tobsec/eidothea/etb-9201.kicad_sch

## KiCad design etb-9201.kicad_sch (2023-04-28)

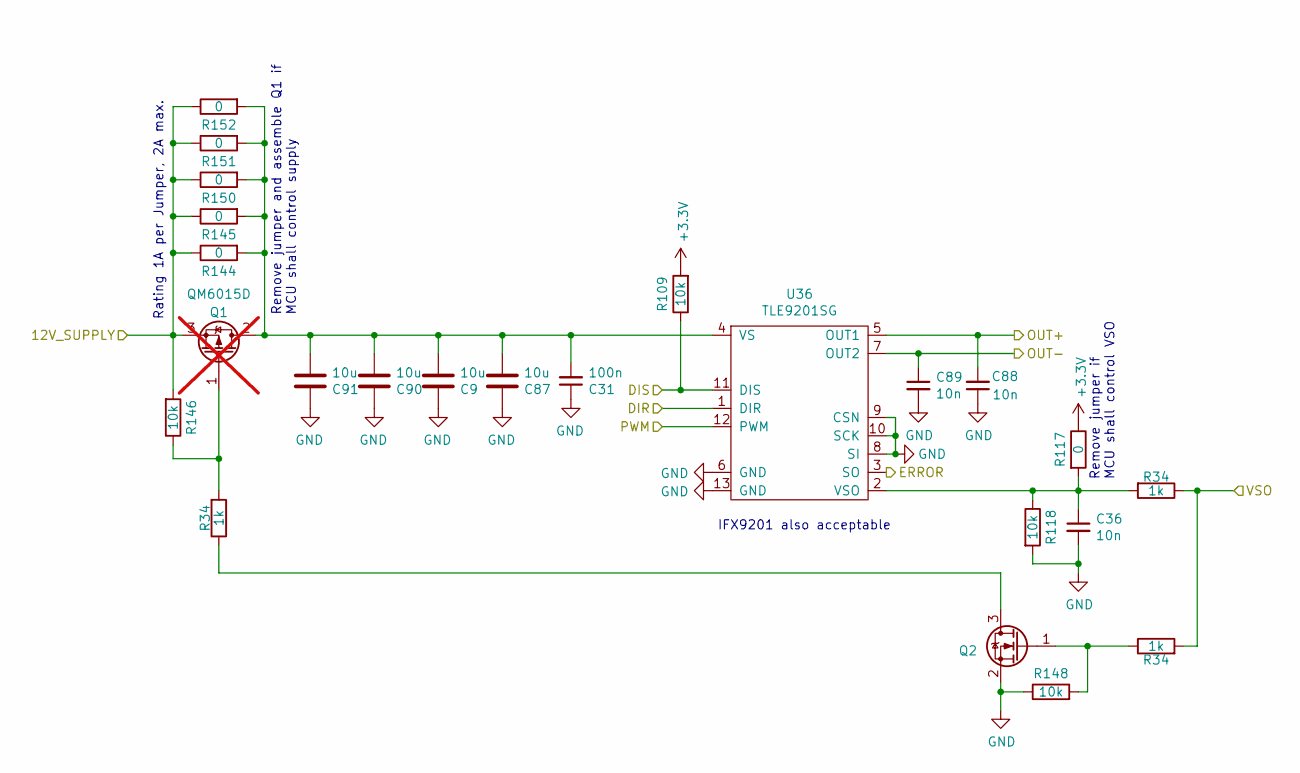
[picture p22: schematic etb-9201.kicad_sch]

Parts:
C9, C87, C90, C91: 10u; C_1206_3216Metric; LCSC C13585
C31: 100n; C_0603_1608Metric; LCSC C14663
C36, C88, C89: 10n; C_0603_1608Metric; LCSC C57112
Q1: QM6015D; TO-252-2; not fitted
Q2: 2N7002; SOT-23; LCSC C8545
R34: 1k; R_0402_1005Metric; LCSC C11702
R109, R118, R146, R148: 10k; R_0402_1005Metric; LCSC C25744
R117, R144, R145, R150, R151, R152: 0; R_0402_1005Metric; LCSC C17168
U36: TLE9201SG; Infineon_PG-DSO-12-9_ThermalVias; LCSC C112633

Connections:
12V_SUPPLY: Q1.3 (S), R144.1, R145.1, R146.2, R150.1, R151.1, R152.1
+3.3V: R109.2, R117.1
DIR: U36.1 (DIR)
DIS: R109.1, U36.11 (DIS)
ERROR: U36.3 (SO)
GND: C9.1, C31.1, C36.2, C87.1, C88.1, C89.2, C90.1, C91.1, Q2.2 (S), R118.2, R148.1, U36.6 (GND), U36.8 (SI), U36.9 (CSN), U36.10 (SCK), U36.13 (GND)
unnamed: C9.2, C31.2, C87.2, C90.2, C91.2, Q1.2 (D), R144.2, R145.2, R150.2, R151.2, R152.2, U36.4 (VS)
unnamed: C36.1, R34.2, R117.2, R118.1, U36.2 (VSO)
unnamed: Q1.1 (G), R34.2, R146.1
unnamed: Q2.1 (G), R34.1, R148.2
unnamed: Q2.3 (D), R34.1
OUT+: C88.2, U36.5 (OUT1)
OUT-: C89.1, U36.7 (OUT2)
PWM: U36.12 (PWM)
VSO: R34.1, R34.2

Notes on the sheet:
Remove jumper and assemble Q1 if MCU shall control supply
IFX9201 also acceptable
Rating 1A per Jumper, 2A max.
Remove jumper if MCU shall control VSO
