tobsec/eidothea/etbsupervisor.kicad_sch

## KiCad design etbsupervisor.kicad_sch (2023-04-28)

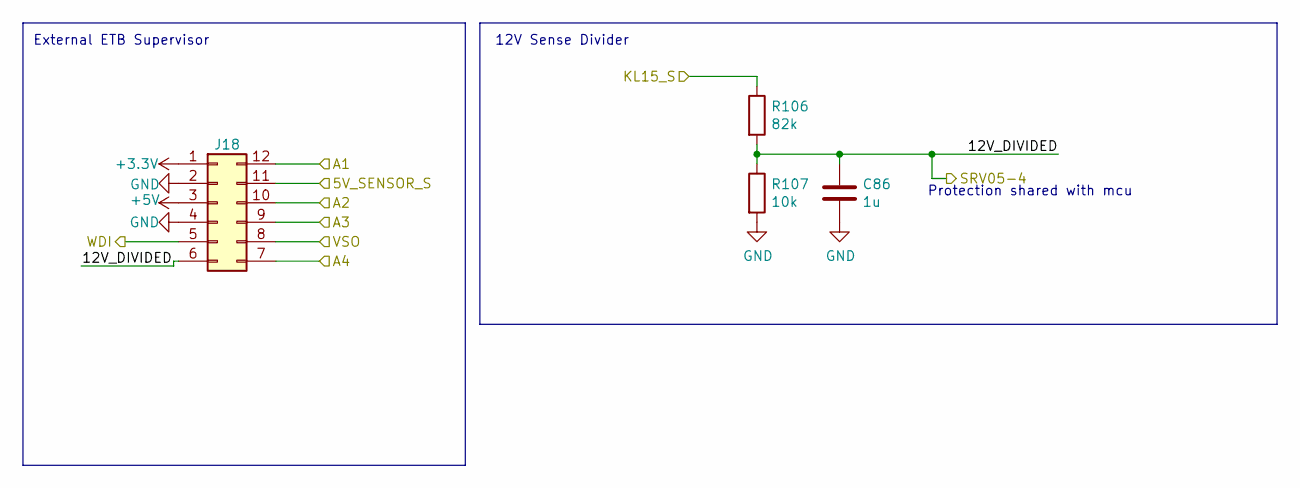
[picture p23: schematic etbsupervisor.kicad_sch]

Parts:
C86: 1u; C_0603_1608Metric; LCSC C15849
J18: Conn_02x04_Counter_Clockwise; PinHeader_2x06_P2.54mm_Vertical
R106: 82k; R_0603_1608Metric; LCSC C23254
R107: 10k; R_0402_1005Metric; LCSC C25744

Connections:
5V_SENSOR_S: J18.11
12V_DIVIDED: C86.1, J18.6, R106.2, R107.1
+3.3V: J18.1
+5V: J18.3
A1: J18.12
A2: J18.10
A3: J18.9
A4: J18.7
GND: C86.2, J18.2, J18.4, R107.2
KL15_S: R106.1
VSO: J18.8
WDI: J18.5

Notes on the sheet:
Protection shared with mcu
External ETB Supervisor
12V Sense Divider
