tobsec/eidothea/ign4.kicad_sch

## KiCad design ign4.kicad_sch (2023-04-26)

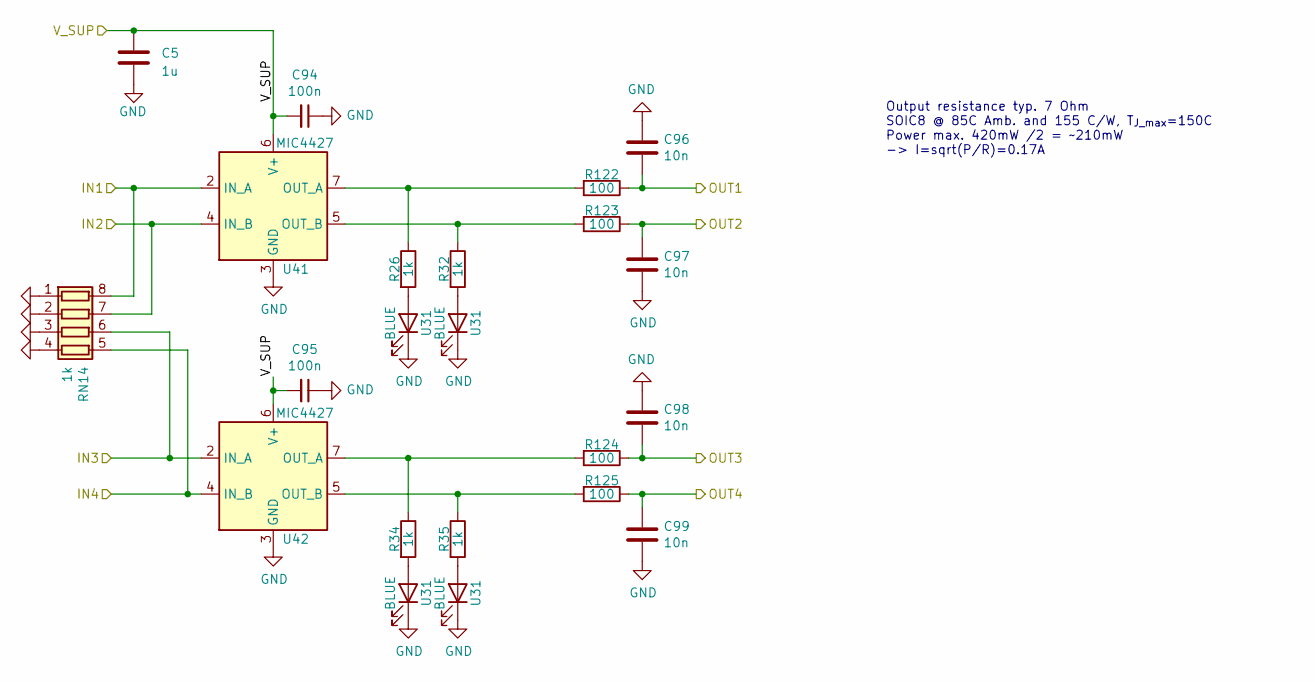
[picture p24: schematic ign4.kicad_sch]

Parts:
C5: 1u; C_0603_1608Metric; LCSC C15849
C94, C95: 100n; C_0603_1608Metric; LCSC C14663
C96, C97, C98, C99: 10n; C_0603_1608Metric; LCSC C57112
R26, R32, R34, R35: 1k; R_0402_1005Metric; LCSC C11702
R122, R123, R124, R125: 100; R_2512_6332Metric; LCSC C2907569
RN14: 1k; R_Array_Convex_4x0603; LCSC C20197
U31: BLUE; LED_0603_1608Metric; LCSC C72041
U41, U42: MIC4427; SOIC-8_3.9x4.9mm_P1.27mm; LCSC C20551

Connections:
GND: C5.1, C94.1, C95.1, C96.2, C97.2, C98.2, C99.2, RN14.1 (R1.1), RN14.2 (R2.1), RN14.3 (R3.1), RN14.4 (R4.1), U31.1 (K), U41.3 (GND), U42.3 (GND)
IN1: RN14.8 (R1.2), U41.2 (IN_A)
IN2: RN14.7 (R2.2), U41.4 (IN_B)
IN3: RN14.6 (R3.2), U42.2 (IN_A)
IN4: RN14.5 (R4.2), U42.4 (IN_B)
unnamed: R26.2, U31.2 (A)
unnamed: R32.2, U31.2 (A)
unnamed: R34.2, U31.2 (A)
unnamed: R35.2, U31.2 (A)
unnamed: R26.1, R122.2, U41.7 (OUT_A)
unnamed: R32.1, R123.2, U41.5 (OUT_B)
unnamed: R34.1, R124.2, U42.7 (OUT_A)
unnamed: R35.1, R125.2, U42.5 (OUT_B)
OUT1: C96.1, R122.1
OUT2: C97.1, R123.1
OUT3: C98.1, R124.1
OUT4: C99.1, R125.1
V_SUP: C5.2, C94.2, C95.2, U41.6 (V+), U42.6 (V+)

Notes on the sheet:
Output resistance typ. 7 Ohm SOIC8 @ 85C Amb. and 155 C/W, T_{J_max}=150C Power max. 420mW /2 = ~210mW -> I=sqrt(P/R)=0.17A
