tobsec/eidothea/knock.kicad_sch

## KiCad design knock.kicad_sch (2023-04-28)

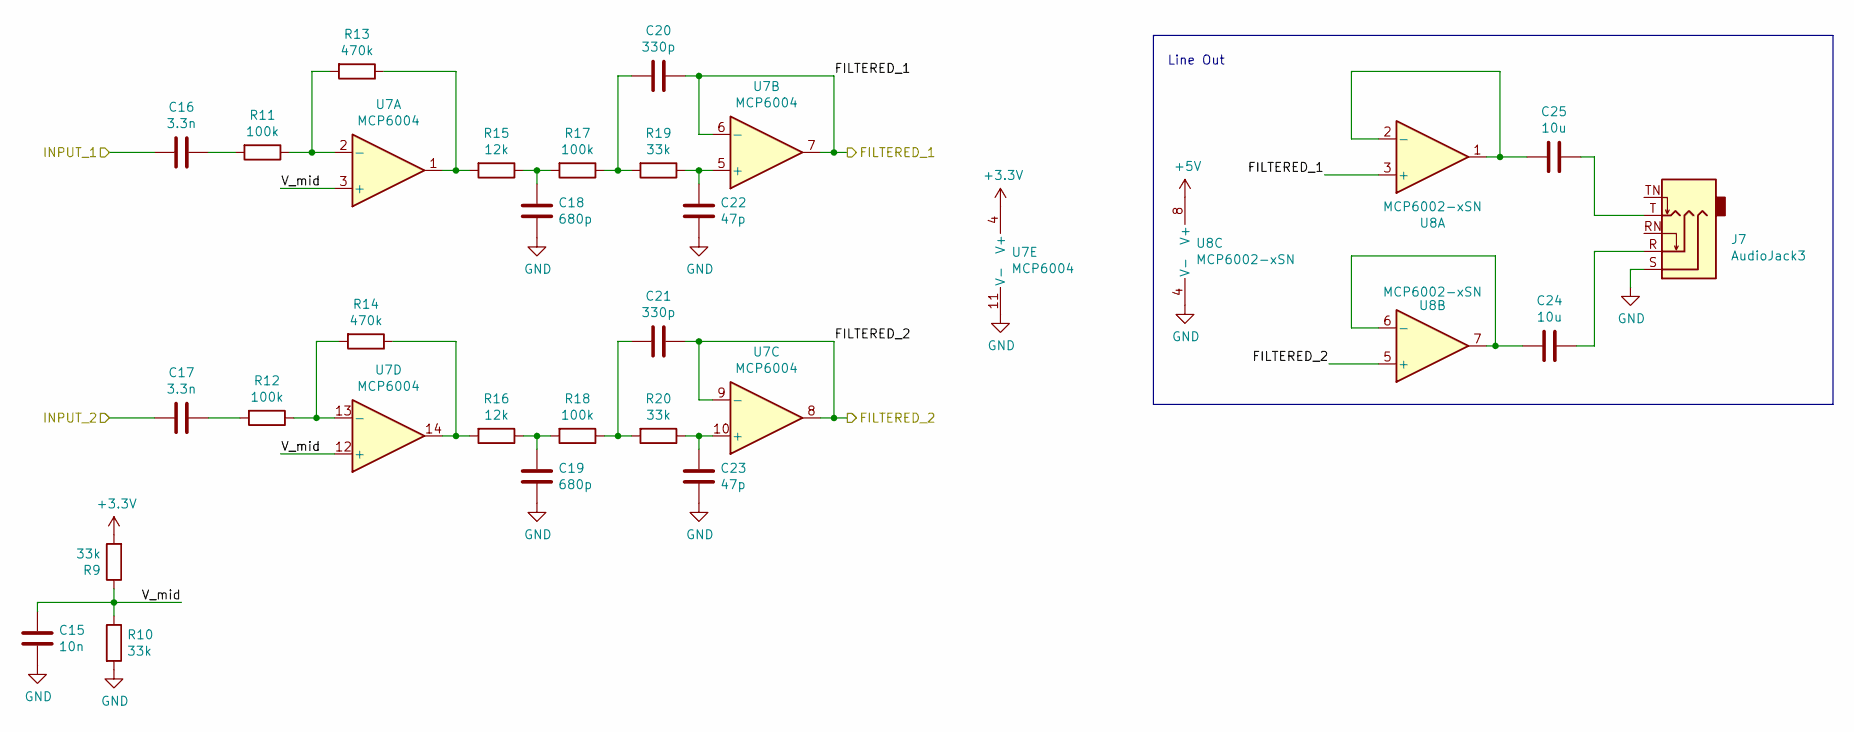
[picture p25: schematic knock.kicad_sch]

Parts:
C15: 10n; C_0603_1608Metric; LCSC C57112
C16, C17: 3.3n; C_0805_2012Metric; LCSC C107149
C18, C19: 680p; C_0603_1608Metric; LCSC C1630
C20, C21: 330p; C_0402_1005Metric; LCSC C13533
C22, C23: 47p; C_0402_1005Metric; LCSC C1567
C24, C25: 10u; C_1206_3216Metric; LCSC C13585
J7: AudioJack3; Jack_3.5mm_PJ-3250-5A; LCSC C165947
R9, R10, R19, R20: 33k; R_0402_1005Metric; LCSC C25779
R11, R12, R17, R18: 100k; R_0402_1005Metric; LCSC C25741
R13, R14: 470k; R_0402_1005Metric; LCSC C25790
R15, R16: 12k; R_0402_1005Metric; LCSC C25752
U7: MCP6004; TSSOP-14_4.4x5mm_P0.65mm; LCSC C50282
U8: MCP6002-xSN; SOIC-8_3.9x4.9mm_P1.27mm; LCSC C7377

Connections:
+3.3V: R9.2, U7.4 (V+)
+5V: U8.8 (V+)
FILTERED_1: C20.2, U7.6 (-), U7.7, U8.3 (+)
FILTERED_2: C21.2, U7.8, U7.9 (-), U8.5 (+)
GND: C15.1, C18.1, C19.1, C22.1, C23.1, J7.S, R10.2, U7.11 (V-), U8.4 (V-)
INPUT_1: C16.2
INPUT_2: C17.2
unnamed: C16.1, R11.2
unnamed: C17.1, R12.2
unnamed: C18.2, R15.1, R17.2
unnamed: C19.2, R16.1, R18.2
unnamed: C20.1, R17.1, R19.2
unnamed: C21.1, R18.1, R20.2
unnamed: C22.2, R19.1, U7.5 (+)
unnamed: C23.2, R20.1, U7.10 (+)
unnamed: C24.1, J7.R
unnamed: C24.2, U8.6 (-), U8.7
unnamed: C25.1, J7.T
unnamed: C25.2, U8.1, U8.2 (-)
unnamed: R11.1, R13.2, U7.2 (-)
unnamed: R12.1, R14.2, U7.13 (-)
unnamed: R13.1, R15.2, U7.1
unnamed: R14.1, R16.2, U7.14
V_mid: C15.2, R9.1, R10.1, U7.3 (+), U7.12 (+)

Notes on the sheet:
Line Out
