tobsec/eidothea/lowside_dual.kicad_sch

## KiCad design lowside_dual.kicad_sch (2023-04-28)

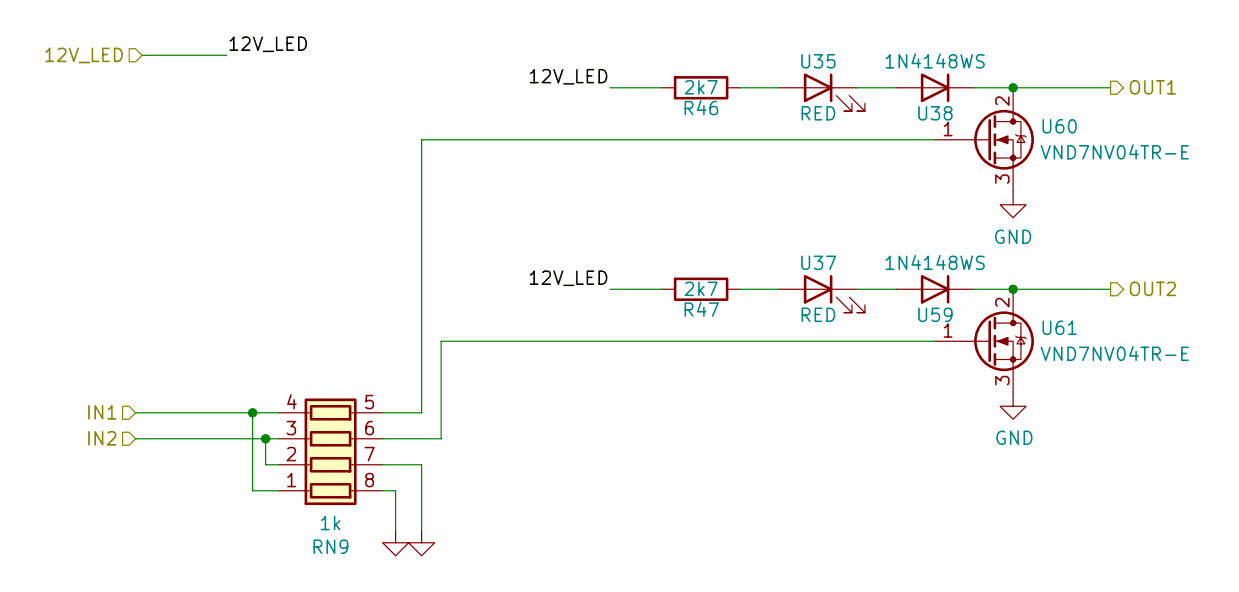
[picture p26: schematic lowside_dual.kicad_sch]

Parts:
R46, R47: 2k7; R_0402_1005Metric; LCSC C138017
RN9: 1k; R_Array_Convex_4x0603; LCSC C20197
U35, U37: RED; LED_0603_1608Metric; LCSC C2286
U38, U59: 1N4148WS; D_SOD-323; LCSC C2128
U60, U61: VND7NV04TR-E; TO-252-3_TabPin2; LCSC C262999

Connections:
12V_LED: R46.2, R47.2
GND: RN9.7 (R2.2), RN9.8 (R1.2), U60.3 (S), U61.3 (S)
IN1: RN9.1 (R1.1), RN9.4 (R4.1)
IN2: RN9.2 (R2.1), RN9.3 (R3.1)
unnamed: R46.1, U35.2 (A)
unnamed: R47.1, U37.2 (A)
unnamed: RN9.5 (R4.2), U60.1 (G)
unnamed: RN9.6 (R3.2), U61.1 (G)
unnamed: U35.1 (K), U38.2 (A)
unnamed: U37.1 (K), U59.2 (A)
OUT1: U38.1 (K), U60.2 (D)
OUT2: U59.1 (K), U61.2 (D)
