tobsec/eidothea/lowside_quad.kicad_sch

## KiCad design lowside_quad.kicad_sch (2023-04-28)

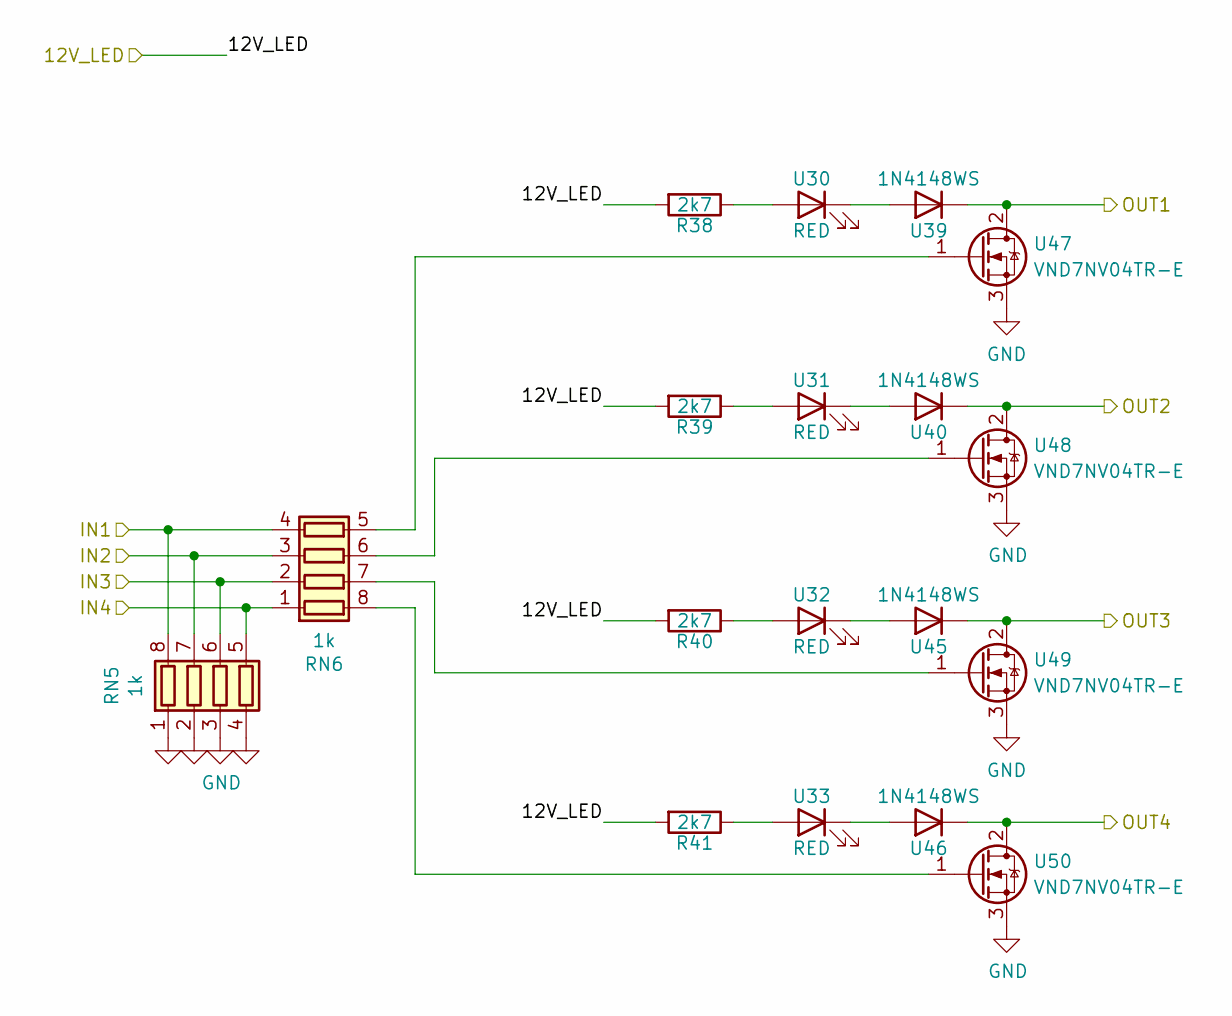
[picture p27: schematic lowside_quad.kicad_sch]

Parts:
R38, R39, R40, R41: 2k7; R_0402_1005Metric; LCSC C138017
RN5, RN6: 1k; R_Array_Convex_4x0603; LCSC C20197
U30, U31, U32, U33: RED; LED_0603_1608Metric; LCSC C2286
U39, U40, U45, U46: 1N4148WS; D_SOD-323; LCSC C2128
U47, U48, U49, U50: VND7NV04TR-E; TO-252-3_TabPin2; LCSC C262999

Connections:
12V_LED: R38.2, R39.2, R40.2, R41.2
GND: RN5.1 (R1.1), RN5.2 (R2.1), RN5.3 (R3.1), RN5.4 (R4.1), U47.3 (S), U48.3 (S), U49.3 (S), U50.3 (S)
IN1: RN5.8 (R1.2), RN6.4 (R4.1)
IN2: RN5.7 (R2.2), RN6.3 (R3.1)
IN3: RN5.6 (R3.2), RN6.2 (R2.1)
IN4: RN5.5 (R4.2), RN6.1 (R1.1)
unnamed: R38.1, U30.2 (A)
unnamed: R39.1, U31.2 (A)
unnamed: R40.1, U32.2 (A)
unnamed: R41.1, U33.2 (A)
unnamed: RN6.5 (R4.2), U47.1 (G)
unnamed: RN6.6 (R3.2), U48.1 (G)
unnamed: RN6.7 (R2.2), U49.1 (G)
unnamed: RN6.8 (R1.2), U50.1 (G)
unnamed: U30.1 (K), U39.2 (A)
unnamed: U31.1 (K), U40.2 (A)
unnamed: U32.1 (K), U45.2 (A)
unnamed: U33.1 (K), U46.2 (A)
OUT1: U39.1 (K), U47.2 (D)
OUT2: U40.1 (K), U48.2 (D)
OUT3: U45.1 (K), U49.2 (D)
OUT4: U46.1 (K), U50.2 (D)
