tobsec/eidothea/lowside_uln2003.kicad_sch

## KiCad design lowside_uln2003.kicad_sch (2023-04-26)

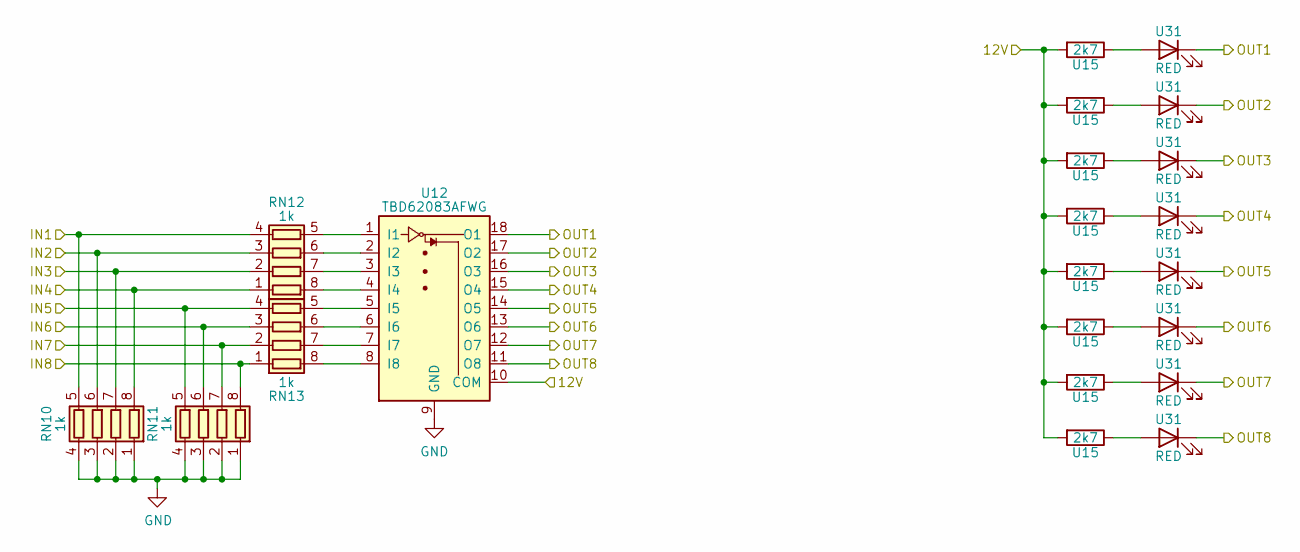
[picture p28: schematic lowside_uln2003.kicad_sch]

Parts:
RN10, RN11, RN12, RN13: 1k; R_Array_Convex_4x0603; LCSC C20197
U12: TBD62083AFWG; SOIC-18W_7.5x11.6mm_P1.27mm
U15: 2k7; R_0402_1005Metric; LCSC C138017
U31: RED; LED_0603_1608Metric; LCSC C2286

Connections:
12V: U12.10 (COM), U15.2
GND: RN10.1 (R1.1), RN10.2 (R2.1), RN10.3 (R3.1), RN10.4 (R4.1), RN11.1 (R1.1), RN11.2 (R2.1), RN11.3 (R3.1), RN11.4 (R4.1), U12.9 (GND)
IN1: RN10.5 (R4.2), RN12.4 (R4.1)
IN2: RN10.6 (R3.2), RN12.3 (R3.1)
IN3: RN10.7 (R2.2), RN12.2 (R2.1)
IN4: RN10.8 (R1.2), RN12.1 (R1.1)
IN5: RN11.5 (R4.2), RN13.4 (R4.1)
IN6: RN11.6 (R3.2), RN13.3 (R3.1)
IN7: RN11.7 (R2.2), RN13.2 (R2.1)
IN8: RN11.8 (R1.2), RN13.1 (R1.1)
unnamed: RN12.5 (R4.2), U12.1 (I1)
unnamed: RN12.6 (R3.2), U12.2 (I2)
unnamed: RN12.7 (R2.2), U12.3 (I3)
unnamed: RN12.8 (R1.2), U12.4 (I4)
unnamed: RN13.5 (R4.2), U12.5 (I5)
unnamed: RN13.6 (R3.2), U12.6 (I6)
unnamed: RN13.7 (R2.2), U12.7 (I7)
unnamed: RN13.8 (R1.2), U12.8 (I8)
unnamed: U15.1, U31.2 (A)
OUT1: U12.18 (O1), U31.1 (K)
OUT2: U12.17 (O2), U31.1 (K)
OUT3: U12.16 (O3), U31.1 (K)
OUT4: U12.15 (O4), U31.1 (K)
OUT5: U12.14 (O5), U31.1 (K)
OUT6: U12.13 (O6), U31.1 (K)
OUT7: U12.12 (O7), U31.1 (K)
OUT8: U12.11 (O8), U31.1 (K)
