tobsec/eidothea/mcu.kicad_sch

## KiCad design mcu.kicad_sch (2023-04-28)

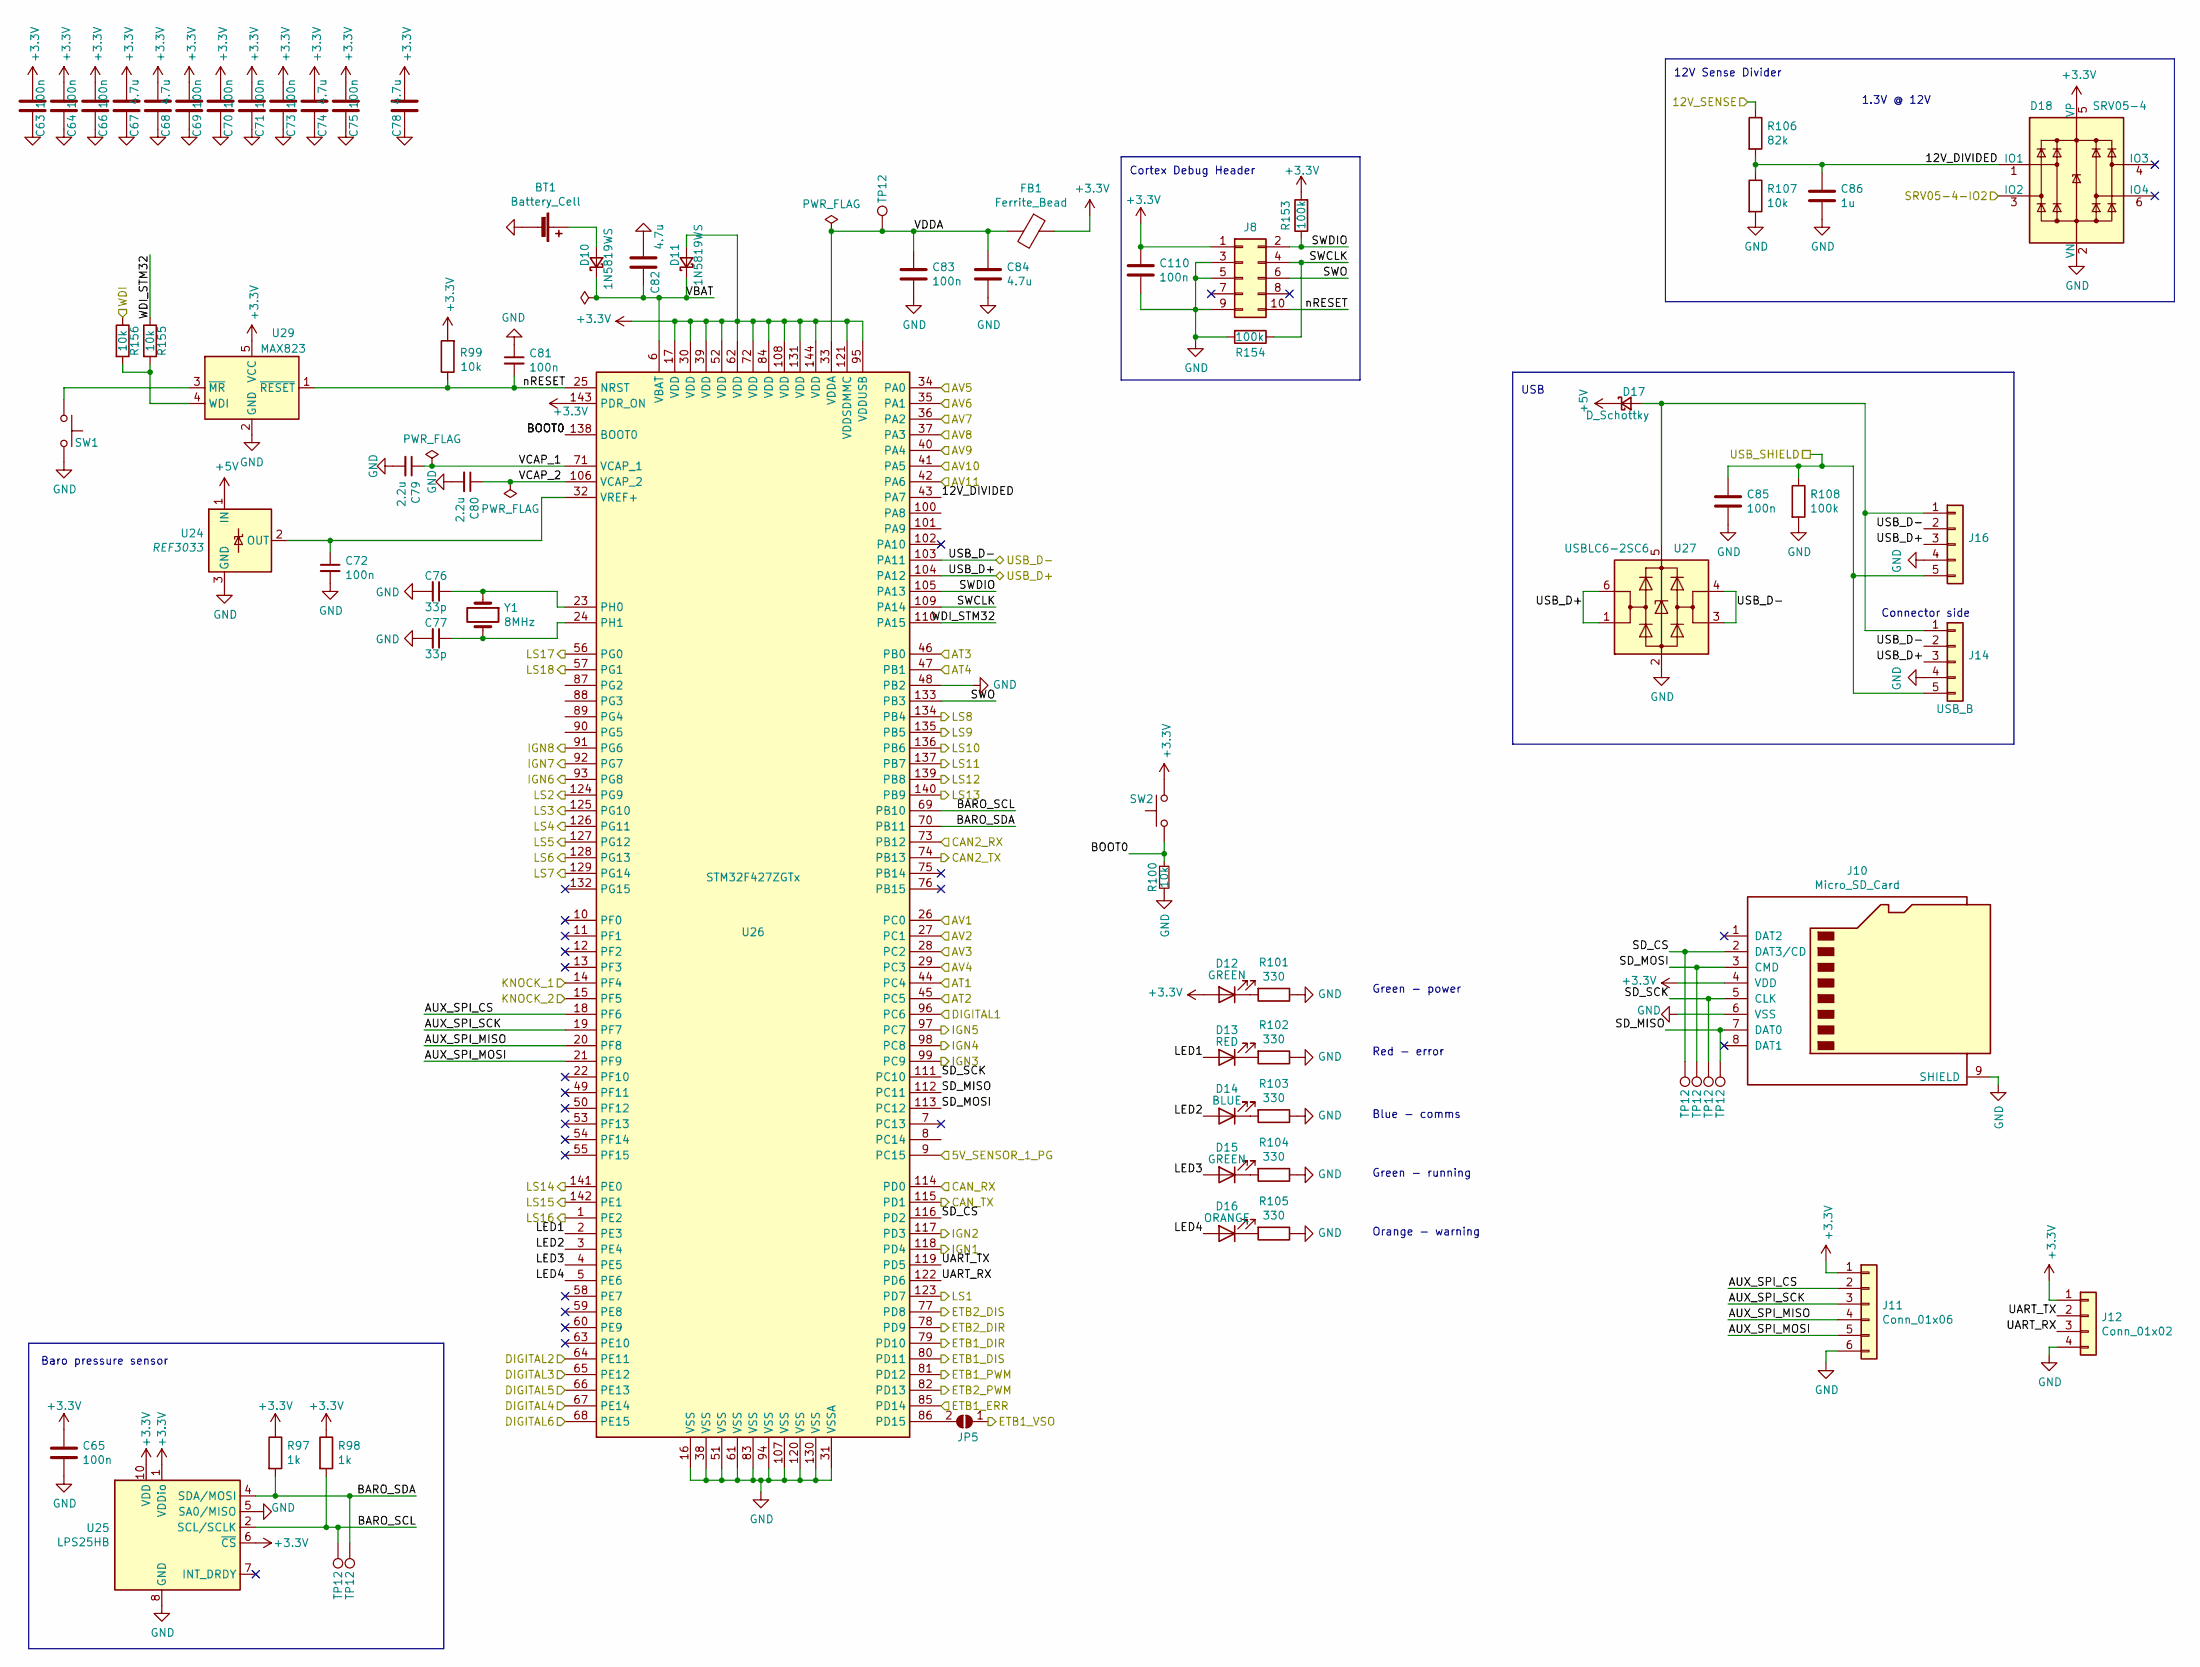
[picture p29: schematic mcu.kicad_sch]

Parts:
BT1: Battery_Cell; BatteryHolder_Keystone_1060_1x2032; LCSC C70377
C63, C64, C65, C66, C69, C70, C71, C72, C73, C75, C81, C83, C85, C110: 100n; C_0603_1608Metric; LCSC C14663
C67, C68, C74, C78, C82, C84: 4.7u; C_0603_1608Metric; LCSC C19666
C76, C77: 33p; C_0402_1005Metric; LCSC C1562
C79, C80: 2.2u; C_0603_1608Metric; LCSC C23630
C86: 1u; C_0603_1608Metric; LCSC C15849
D10, D11: 1N5819WS; D_SOD-323; LCSC C191023
D12, D15: GREEN; LED_0603_1608Metric; LCSC C72043
D13: RED; LED_0603_1608Metric; LCSC C2286
D14: BLUE; LED_0603_1608Metric; LCSC C72041
D16: ORANGE; LED_0603_1608Metric; LCSC C72038
D17: D_Schottky; D_SMA; LCSC C14996
D18: SRV05-4; SOT-23-6; LCSC C85364
FB1: Ferrite_Bead; L_0805_2012Metric; LCSC C1015
J8: Conn_02x05_Odd_Even; PinHeader_2x05_P2.54mm_Vertical; LCSC N/A
J10: Micro_SD_Card; microSD_HC_Wuerth_693072010801; LCSC C164170
J11: Conn_01x06; PinHeader_1x06_P2.54mm_Vertical; LCSC N/A
J12: Conn_01x02; PinHeader_1x04_P2.54mm_Vertical; LCSC N/A
J14: USB_B; USB_B_921-111A1010Y10200_Vertical; LCSC C26234
J16: PinHeader_1x05_P2.54mm_Vertical; JLCPosOffset -1.27,-2.1
JP5: Jumper_2_Bridged; SolderJumper-2_P1.3mm_Open_RoundedPad1.0x1.5mm
R97, R98: 1k; R_0402_1005Metric; LCSC C11702
R99, R100, R107, R155, R156: 10k; R_0402_1005Metric; LCSC C25744
R101, R102, R103, R104, R105: 330; R_0402_1005Metric; LCSC C25104
R106: 82k; R_0603_1608Metric; LCSC C23254
R108, R153, R154: 100k; R_0402_1005Metric; LCSC C25741
SW1, SW2: SW_Push; SW_SPST_EVQQ2; LCSC C318884
TP12: TestPoint; TestPoint_Pad_D1.0mm
U24: REF3033; SOT-23; LCSC C36658
U25: LPS25HB; ST_HLGA-10_2.5x2.5mm_P0.6mm_LayoutBorder3x2y; LCSC C94049
U26: STM32F427ZGTx; LQFP-144_20x20mm_P0.5mm; LCSC C117816
U27: USBLC6-2SC6; SOT-23-6; LCSC C7519
U29: MAX823; SOT-23-5; LCSC C239902
Y1: 8MHz; Crystal_SMD_5032-2Pin_5.0x3.2mm; LCSC C115962

Connections:
5V_SENSOR_1_PG: U26.9 (PC15)
12V_DIVIDED: C86.1, D18.1 (IO1), R106.2, R107.1, U26.43 (PA7)
12V_SENSE: R106.1
+3.3V: C63.2, C64.2, C65.1, C66.2, C67.2, C68.2, C69.2, C70.2, C71.2, C73.2, C74.2, C75.2, C78.2, C110.1, D11.2 (A), D12.2 (A), D18.5 (VP), FB1.1, J8.1, J10.4 (VDD), J11.1, J12.1, R97.1, R98.1, R99.2, R153.2, SW2.2, U25.1 (VDDio), U25.6 (~CS), U25.10 (VDD), U26.17 (VDD), U26.30 (VDD), U26.39 (VDD), U26.52 (VDD), U26.62 (VDD), U26.72 (VDD), U26.84 (VDD), U26.95 (VDDUSB), U26.108 (VDD), U26.121 (VDDSDMMC), U26.131 (VDD), U26.143 (PDR_ON), U26.144 (VDD), U29.5 (VCC)
+5V: D17.1 (K), U24.1 (IN)
AT1: U26.44 (PC4)
AT2: U26.45 (PC5)
AT3: U26.46 (PB0)
AT4: U26.47 (PB1)
AUX_SPI_CS: J11.2, U26.18 (PF6)
AUX_SPI_MISO: J11.4, U26.20 (PF8)
AUX_SPI_MOSI: J11.5, U26.21 (PF9)
AUX_SPI_SCK: J11.3, U26.19 (PF7)
AV1: U26.26 (PC0)
AV2: U26.27 (PC1)
AV3: U26.28 (PC2)
AV4: U26.29 (PC3)
AV5: U26.34 (PA0)
AV6: U26.35 (PA1)
AV7: U26.36 (PA2)
AV8: U26.37 (PA3)
AV9: U26.40 (PA4)
AV10: U26.41 (PA5)
AV11: U26.42 (PA6)
BARO_SCL: R98.2, TP12.1, U25.2 (SCL/SCLK), U26.69 (PB10)
BARO_SDA: R97.2, TP12.1, U25.4 (SDA/MOSI), U26.70 (PB11)
BOOT0: R100.1, SW2.1, U26.138 (BOOT0)
CAN2_RX: U26.73 (PB12)
CAN2_TX: U26.74 (PB13)
CAN_RX: U26.114 (PD0)
CAN_TX: U26.115 (PD1)
DIGITAL1: U26.96 (PC6)
DIGITAL2: U26.64 (PE11)
DIGITAL3: U26.65 (PE12)
DIGITAL4: U26.67 (PE14)
DIGITAL5: U26.66 (PE13)
DIGITAL6: U26.68 (PE15)
ETB1_DIR: U26.79 (PD10)
ETB1_DIS: U26.80 (PD11)
ETB1_ERR: U26.85 (PD14)
ETB1_PWM: U26.81 (PD12)
ETB1_VSO: JP5.1 (A)
ETB2_DIR: U26.78 (PD9)
ETB2_DIS: U26.77 (PD8)
ETB2_PWM: U26.82 (PD13)
GND: BT1.2 (-), C63.1, C64.1, C65.2, C66.1, C67.1, C68.1, C69.1, C70.1, C71.1, C72.2, C73.1, C74.1, C75.1, C76.2, C77.2, C78.1, C79.2, C80.2, C81.1, C82.2, C83.2, C84.2, C85.2, C86.2, C110.2, D18.2 (VN), J8.3, J8.5, J8.9, J10.6 (VSS), J10.9 (SHIELD), J11.6, J12.4, J14.4, J16.4, R100.2, R101.1, R102.1, R103.1, R104.1, R105.1, R107.2, R108.2, R154.2, SW1.2, U24.3 (GND), U25.3 (GND), U25.5 (SA0/MISO), U25.8 (GND), U25.9 (GND), U26.16 (VSS), U26.31 (VSSA), U26.38 (VSS), U26.48 (PB2), U26.51 (VSS), U26.61 (VSS), U26.83 (VSS), U26.94 (VSS), U26.107 (VSS), U26.120 (VSS), U26.130 (VSS), U27.2 (GND), U29.2 (GND)
IGN1: U26.118 (PD4)
IGN2: U26.117 (PD3)
IGN3: U26.99 (PC9)
IGN4: U26.98 (PC8)
IGN5: U26.97 (PC7)
IGN6: U26.93 (PG8)
IGN7: U26.92 (PG7)
IGN8: U26.91 (PG6)
KNOCK_1: U26.14 (PF4)
KNOCK_2: U26.15 (PF5)
LED1: D13.2 (A), U26.2 (PE3)
LED2: D14.2 (A), U26.3 (PE4)
LED3: D15.2 (A), U26.4 (PE5)
LED4: D16.2 (A), U26.5 (PE6)
LS1: U26.123 (PD7)
LS2: U26.124 (PG9)
LS3: U26.125 (PG10)
LS4: U26.126 (PG11)
LS5: U26.127 (PG12)
LS6: U26.128 (PG13)
LS7: U26.129 (PG14)
LS8: U26.134 (PB4)
LS9: U26.135 (PB5)
LS10: U26.136 (PB6)
LS11: U26.137 (PB7)
LS12: U26.139 (PB8)
LS13: U26.140 (PB9)
LS14: U26.141 (PE0)
LS15: U26.142 (PE1)
LS16: U26.1 (PE2)
LS17: U26.56 (PG0)
LS18: U26.57 (PG1)
unnamed: BT1.1 (+), D10.2 (A)
unnamed: C72.1, U24.2 (OUT), U26.32 (VREF+)
unnamed: C76.1, U26.23 (PH0), Y1.1
unnamed: C77.1, U26.24 (PH1), Y1.2
unnamed: D12.1 (K), R101.2
unnamed: D13.1 (K), R102.2
unnamed: D14.1 (K), R103.2
unnamed: D15.1 (K), R104.2
unnamed: D16.1 (K), R105.2
unnamed: D17.2 (A), J14.1, J16.1, U27.5 (VBUS)
unnamed: JP5.2 (B), U26.86 (PD15)
unnamed: R155.2, R156.2, U29.4 (WDI)
unnamed: SW1.1, U29.3 (~MR)
SD_CS: J10.2 (DAT3/CD), TP12.1, U26.116 (PD2)
SD_MISO: J10.7 (DAT0), TP12.1, U26.112 (PC11)
SD_MOSI: J10.3 (CMD), TP12.1, U26.113 (PC12)
SD_SCK: J10.5 (CLK), TP12.1, U26.111 (PC10)
SRV05-4-IO2: D18.3 (IO2)
SWCLK: J8.4, R154.1, U26.109 (PA14)
SWDIO: J8.2, R153.1, U26.105 (PA13)
SWO: J8.6, U26.133 (PB3)
UART_RX: J12.3, U26.122 (PD6)
UART_TX: J12.2, U26.119 (PD5)
USB_D+: J14.3, J16.3, U26.104 (PA12), U27.1 (I/O1), U27.6 (I/O1)
USB_D-: J14.2, J16.2, U26.103 (PA11), U27.3 (I/O2), U27.4 (I/O2)
USB_SHIELD: C85.1, J14.5, J16.5, R108.1
VBAT: C82.1, D10.1 (K), D11.1 (K), U26.6 (VBAT)
VCAP_1: C79.1, U26.71 (VCAP_1)
VCAP_2: C80.1, U26.106 (VCAP_2)
VDDA: C83.1, C84.1, FB1.2, TP12.1, U26.33 (VDDA)
WDI: R156.1
WDI_STM32: R155.1, U26.110 (PA15)
nRESET: C81.2, J8.10, R99.1, U26.25 (NRST), U29.1 (~RESET)

Notes on the sheet:
Orange - warning
Connector side
USB
1.3V @ 12V
Cortex Debug Header
Baro pressure sensor
Blue - comms
Green - power
12V Sense Divider
Red - error
Green - running
