tobsec/eidothea/proteus.kicad_sch

## KiCad design proteus.kicad_sch (2023-04-28)

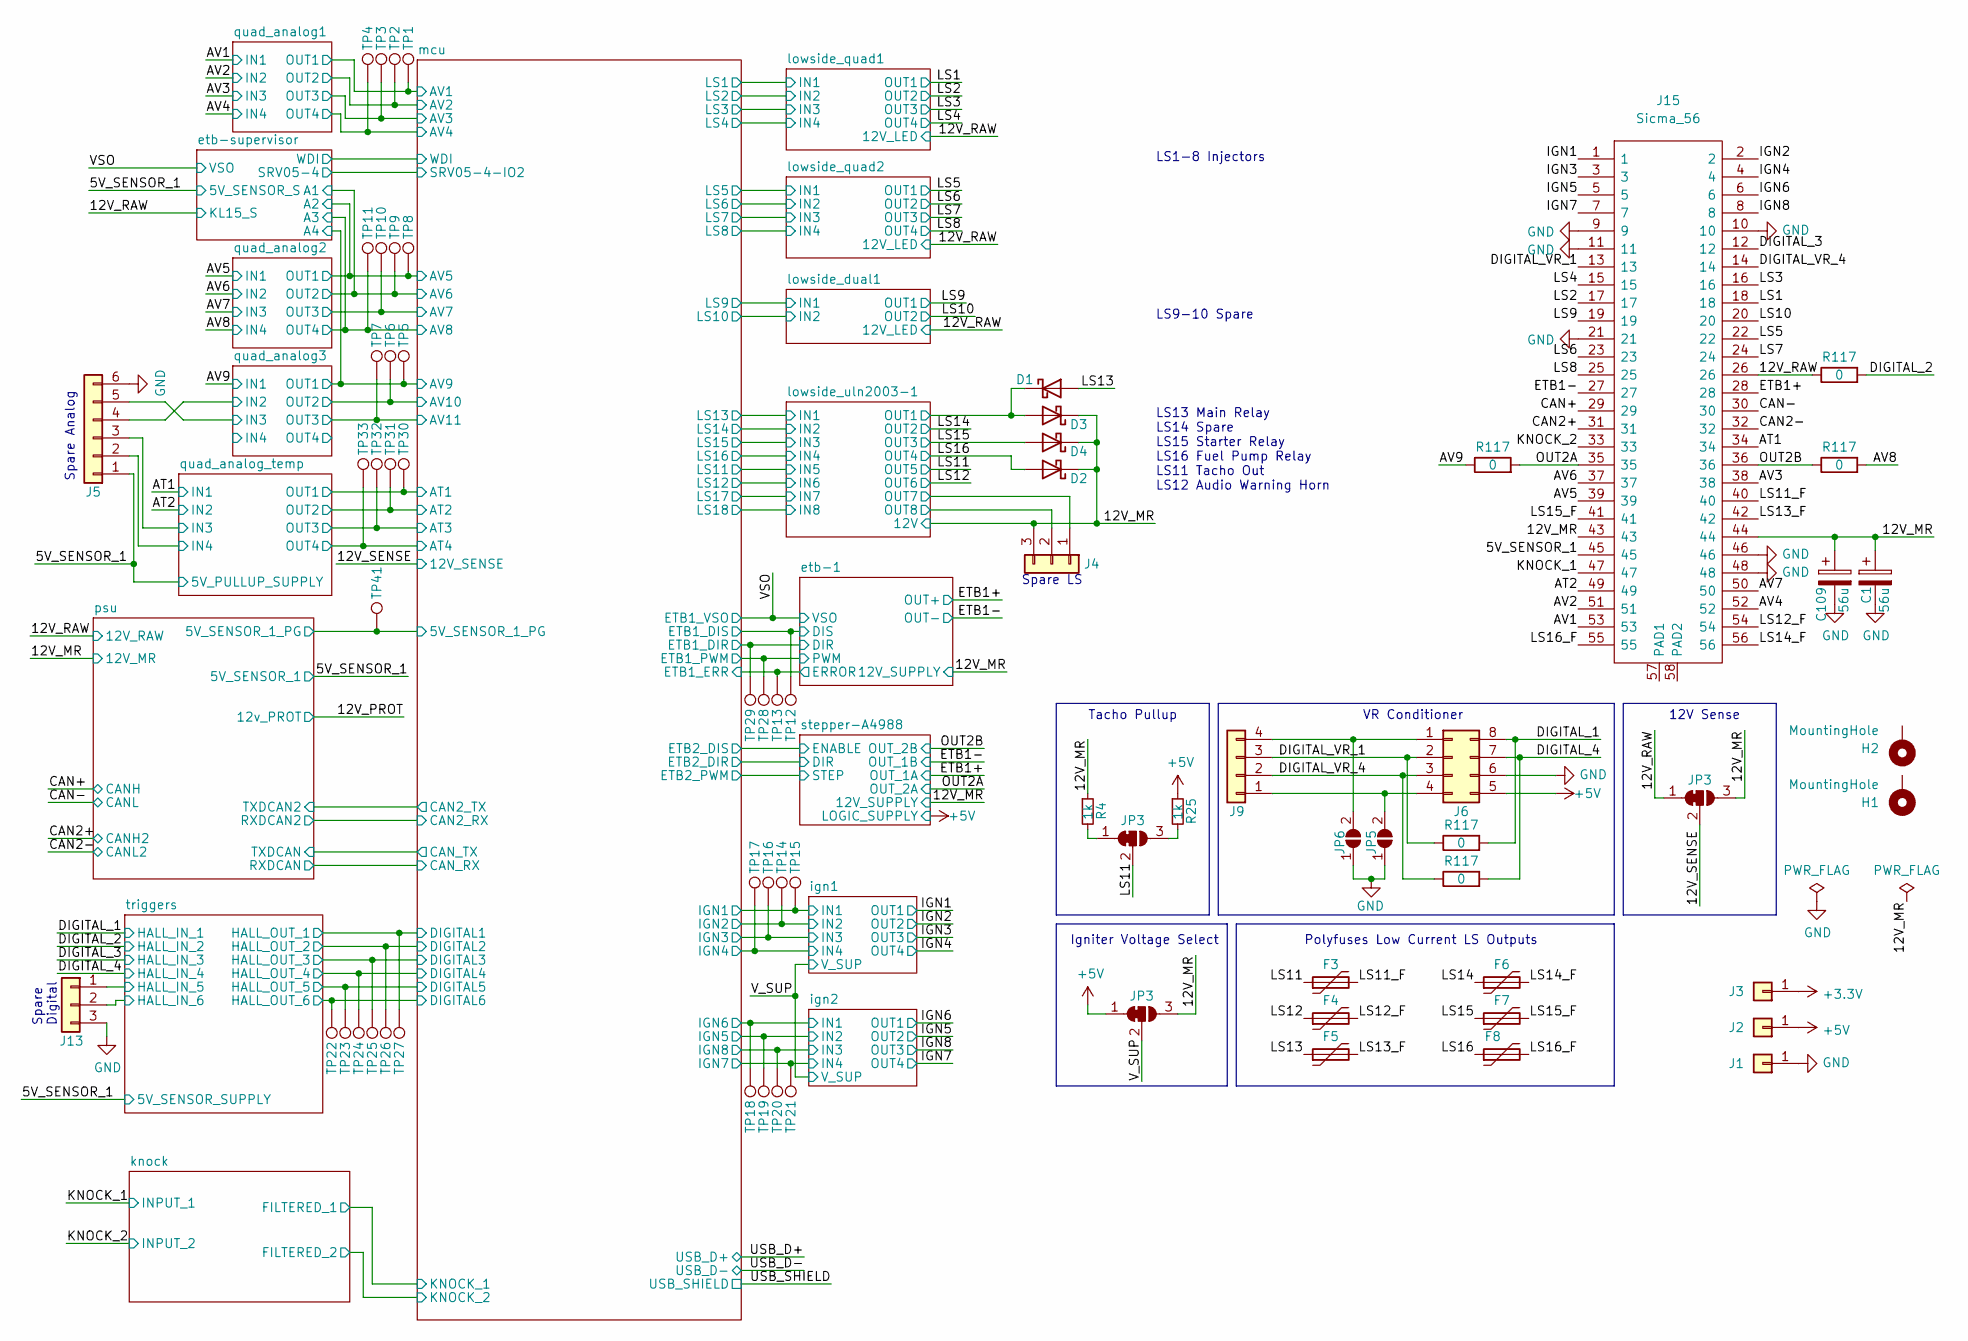
[picture p30: schematic proteus.kicad_sch]

Parts:
C1, C109: 56u; CP_Radial_D8.0mm_P3.50mm; LCSC C106564
D1, D2, D3, D4: D_Schottky; D_SMA; LCSC C14996
F3, F4, F5, F6, F7, F8: Polyfuse; R_1206_3216Metric; LCSC C207035
H1, H2: MountingHole; MountingHole_4mm_Pad_Via
J1, J2, J3: Conn_01x01; TestPoint_Pad_D3.0mm; LCSC N/A
J4, J13: Conn_01x03; PinHeader_1x03_P2.54mm_Vertical
J5: Conn_01x05; PinHeader_1x06_P2.54mm_Vertical
J6: Conn_02x04_Counter_Clockwise; DIP-8_W7.62mm_Socket_VR
J9: Conn_01x04; PinHeader_1x04_P2.54mm_Vertical; LCSC N/A
J15: Sicma_56; Manufacturer_Part_Number 211PL562L0011
JP3: Jumper_3_Bridged12; SolderJumper-3_P1.3mm_Bridged12_RoundedPad1.0x1.5mm
JP5, JP6: Jumper_2_Bridged; SolderJumper-2_P1.3mm_Open_RoundedPad1.0x1.5mm
R4, R25: 1k; R_0402_1005Metric; LCSC C11702
R117: 0; R_0402_1005Metric; LCSC C17168
TP1, TP2, TP3, TP4, TP5, TP6, TP7, TP8, TP9, TP10, TP11, TP12, TP13, TP14, TP15, TP16, TP17, TP18, TP19, TP20, TP21, TP22, TP23, TP24, TP25, TP26, TP27, TP28, TP29, TP30, TP31, TP32, TP33, TP41: TestPoint; TestPoint_Pad_D1.0mm

Connections:
5V_SENSOR_1: J5.1, J15.45
5V_SENSOR_1_PG: TP41.1
12V_MR: C1.1, C109.1, D2.1 (K), D3.1 (K), D4.1 (K), J4.3, J15.43, J15.44, JP3.3 (B), R4.1
12V_RAW: J15.26, JP3.1 (A), R117.1
12V_SENSE: JP3.2 (C)
+3.3V: J3.1
+5V: J2.1, J6.5, JP3.1 (A), R25.1
A1: TP9.1
A2: TP8.1
A3: TP11.1
A4: TP5.1
AT1: J15.34
AT2: J15.49
AV1: J15.53, TP1.1
AV2: J15.51, TP2.1
AV3: J15.38, TP3.1
AV4: J15.52, TP4.1
AV5: J15.39
AV6: J15.37
AV7: J15.50, TP10.1
AV8: R117.2
AV9: R117.1
AV10: TP6.1
AV11: TP7.1
CAN2+: J15.31
CAN2-: J15.32
CAN+: J15.29
CAN-: J15.30
DIGITAL_1: J6.8, R117.2
DIGITAL_2: R117.2
DIGITAL_3: J15.12
DIGITAL_4: J6.7, R117.2
DIGITAL_VR_1: J6.2, J9.3, J15.13, R117.1
DIGITAL_VR_4: J6.3, J9.2, J15.14, R117.1
DIR: TP29.1
DIS: TP12.1
ERROR: TP13.1
ETB1+: J15.28
ETB1-: J15.27
GND: C1.2, C109.2, J1.1, J5.6, J6.6, J13.3, J15.9, J15.10, J15.11, J15.21, J15.46, J15.48, JP5.1 (A), JP6.1 (A)
HALL_IN_5: J13.1
HALL_IN_6: J13.2
HALL_OUT_1: TP27.1
HALL_OUT_2: TP26.1
HALL_OUT_3: TP25.1
HALL_OUT_4: TP24.1
HALL_OUT_5: TP23.1
HALL_OUT_6: TP22.1
IGN1: J15.1
IGN2: J15.2
IGN3: J15.3
IGN4: J15.4
IGN5: J15.5
IGN6: J15.6
IGN7: J15.7
IGN8: J15.8
IN1: TP15.1, TP18.1
IN2: J5.4, TP14.1, TP19.1
IN3: J5.3, J5.5, TP16.1, TP20.1
IN4: J5.2, TP17.1, TP21.1
KNOCK_1: J15.47
KNOCK_2: J15.33
LS1: J15.18
LS2: J15.17
LS3: J15.16
LS4: J15.15
LS5: J15.22
LS6: J15.23
LS7: J15.24
LS8: J15.25
LS9: J15.19
LS10: J15.20
LS11: F3.1, JP3.2 (C)
LS11_F: F3.2, J15.40
LS12: F4.1
LS12_F: F4.2, J15.54
LS13: D1.2 (A), F5.1
LS13_F: F5.2, J15.42
LS14: F6.1
LS14_F: F6.2, J15.56
LS15: D4.2 (A), F7.1
LS15_F: F7.2, J15.41
LS16: D2.2 (A), F8.1
LS16_F: F8.2, J15.55
unnamed: J6.1, J9.4, JP6.2 (B)
unnamed: J6.4, J9.1, JP5.2 (B)
unnamed: JP3.1 (A), R4.2
unnamed: JP3.3 (B), R25.2
OUT1: D1.1 (K), D3.2 (A), TP30.1
OUT2: TP31.1
OUT2A: J15.35, R117.2
OUT2B: J15.36, R117.1
OUT3: TP32.1
OUT4: TP33.1
OUT7: J4.1
OUT8: J4.2
PWM: TP28.1
V_SUP: JP3.2 (C)

Notes on the sheet:
LS9-10 Spare
LS1-8 Injectors
Spare LS
Igniter Voltage Select
VR Conditioner
Spare Digital
Tacho Pullup
12V Sense
Polyfuses Low Current LS Outputs
LS13 Main Relay LS14 Spare LS15 Starter Relay LS16 Fuel Pump Relay LS11 Tacho Out LS12 Audio Warning Horn
Spare Analog
