tobsec/eidothea/psu.kicad_sch

## KiCad design psu.kicad_sch (2023-04-28)

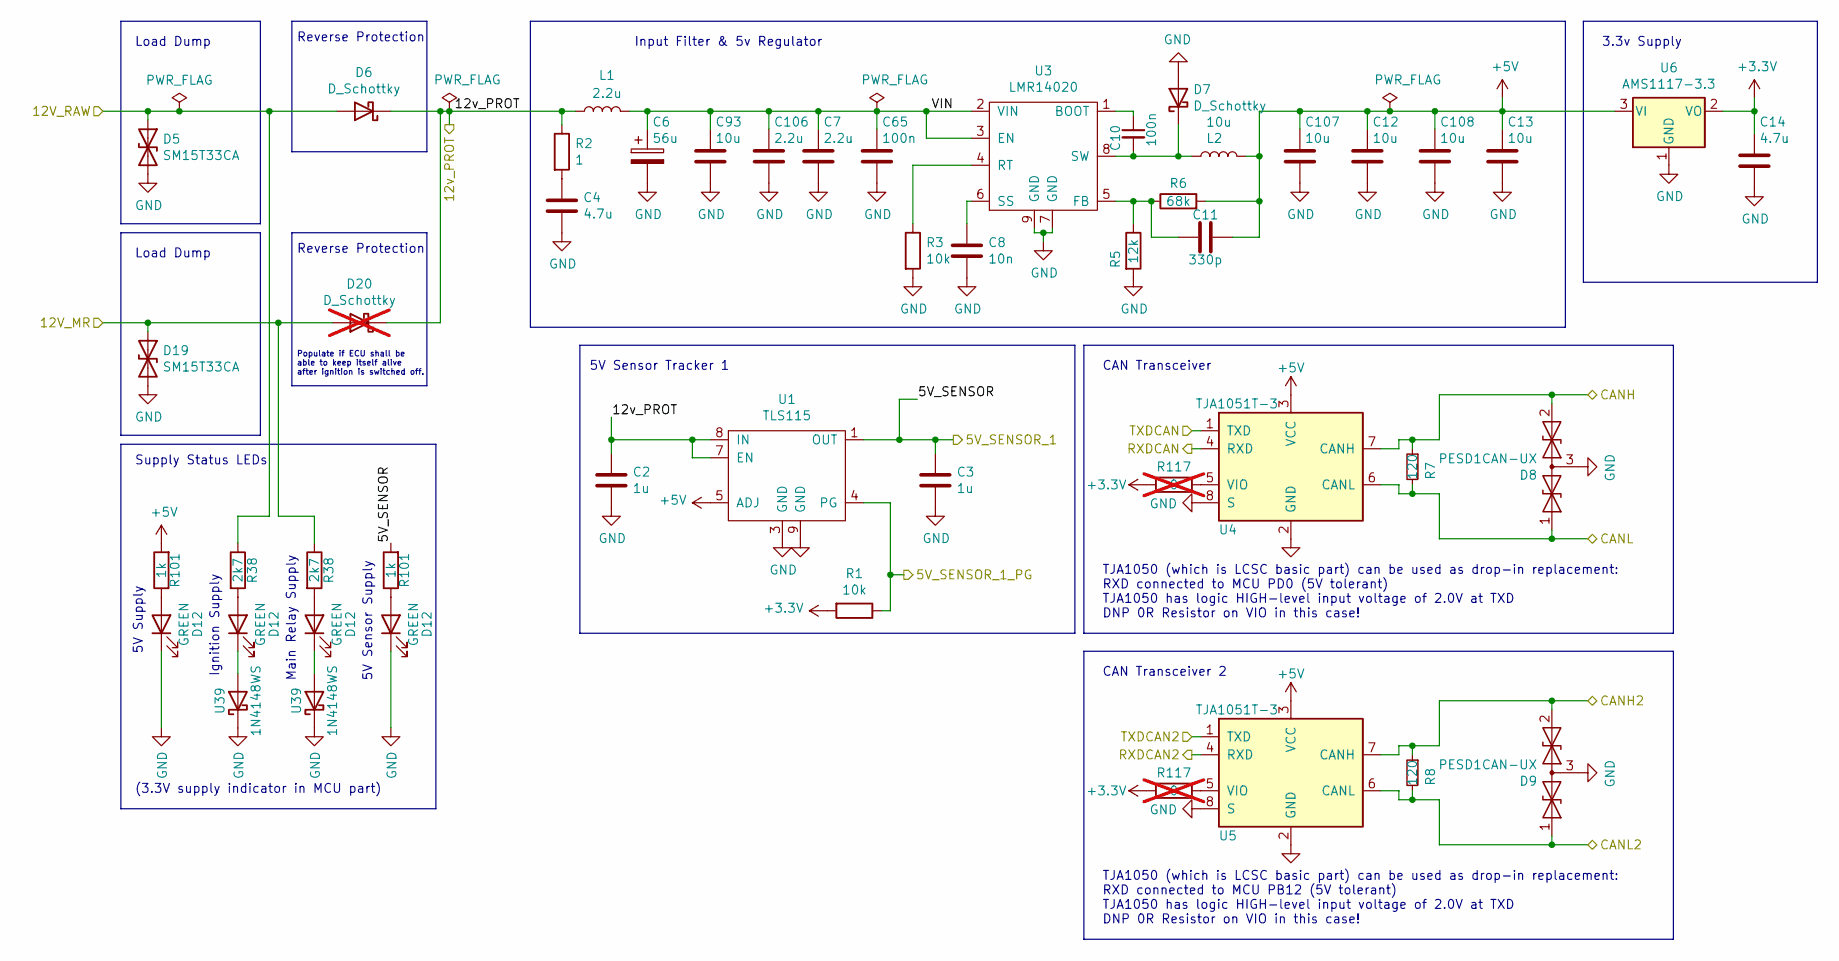
[picture p31: schematic psu.kicad_sch]

Parts:
C2, C3: 1u; C_0603_1608Metric; LCSC C15849
C4: 4.7u; C_0805_2012Metric; LCSC C98192
C6: 56u; CP_Radial_D8.0mm_P3.50mm; LCSC C106564
C7, C106: 2.2u; C_1206_3216Metric; LCSC C170101
C8: 10n; C_0603_1608Metric; LCSC C57112
C10, C65: 100n; C_0603_1608Metric; LCSC C14663
C11: 330p; C_0402_1005Metric; LCSC C13533
C12, C13, C93, C107, C108: 10u; C_1206_3216Metric; LCSC C13585
C14: 4.7u; C_0603_1608Metric; LCSC C19666
D5, D19: SM15T33CA; D_SMC; LCSC C406701
D6, D7: D_Schottky; D_SMA; LCSC C14996
D8, D9: PESD1CAN-UX; SOT-323_SC-70; LCSC C152727
D12: GREEN; LED_0603_1608Metric; LCSC C72043
D20: D_Schottky; D_SMA; LCSC C14996; not fitted
L1: 2.2u; L_1210_3225Metric; LCSC C36828
L2: 10u; MWSA0503; LCSC C408412
R1, R3: 10k; R_0402_1005Metric; LCSC C25744
R2: 1; R_0402_1005Metric; LCSC C25086
R5: 12k; R_0402_1005Metric; LCSC C25752
R6: 68k; R_0402_1005Metric; LCSC C36871
R7, R8: 120; R_0603_1608Metric; LCSC C22787
R38: 2k7; R_0402_1005Metric; LCSC C138017
R101: 1k; R_0402_1005Metric; LCSC C11702
R117: 0; R_0402_1005Metric; LCSC C17168; not fitted
U1: TLS115; Infineon_PG-DSO-8-43; LCSC N/A
U3: LMR14020; SOIC-8-1EP_3.9x4.9mm_P1.27mm_EP2.29x3mm; LCSC C187824
U4, U5: TJA1051T-3; SOIC-8_3.9x4.9mm_P1.27mm; LCSC C6952
U6: AMS1117-3.3; SOT-223-3_TabPin2; LCSC C6186
U39: 1N4148WS; D_SOD-323; LCSC C2128

Connections:
5V_SENSOR: C3.1, R101.2, U1.1 (OUT)
5V_SENSOR_1_PG: R1.1, U1.4 (PG)
12V_MR: D19.1 (A1), D20.2 (A), R38.1
12V_RAW: D5.1 (A1), D6.2 (A), R38.1
12v_PROT: C2.1, D6.1 (K), D20.1 (K), L1.1, R2.1, U1.7 (EN), U1.8 (IN)
+3.3V: C14.1, R1.2, R117.1, U6.2 (VO)
+5V: C11.1, C12.1, C13.1, C107.1, C108.1, L2.2, R6.2, R101.2, U1.5 (ADJ), U4.3 (VCC), U5.3 (VCC), U6.3 (VI)
CANH: D8.2 (A2), R7.1, U4.7 (CANH)
CANH2: D9.2 (A2), R8.1, U5.7 (CANH)
CANL: D8.1 (A1), R7.2, U4.6 (CANL)
CANL2: D9.1 (A1), R8.2, U5.6 (CANL)
GND: C2.2, C3.2, C4.2, C6.2, C7.2, C8.2, C12.2, C13.2, C14.2, C65.2, C93.2, C106.2, C107.2, C108.2, D5.2 (A2), D7.2 (A), D8.3 (common), D9.3 (common), D12.1 (K), D19.2 (A2), R3.2, R5.2, U1.3 (GND), U1.9 (GND), U3.7 (GND), U3.9 (GND), U4.2 (GND), U4.8 (S), U5.2 (GND), U5.8 (S), U6.1 (GND), U39.1 (K)
unnamed: C4.1, R2.2
unnamed: C8.1, U3.6 (SS)
unnamed: C10.1, U3.1 (BOOT)
unnamed: C10.2, D7.1 (K), L2.1, U3.8 (SW)
unnamed: C11.2, R5.1, R6.1, U3.5 (FB)
unnamed: D12.1 (K), U39.2 (A)
unnamed: D12.2 (A), R38.2, R101.1
unnamed: R3.1, U3.4 (RT)
unnamed: R117.2, U4.5 (VIO), U5.5 (VIO)
RXDCAN: U4.4 (RXD)
RXDCAN2: U5.4 (RXD)
TXDCAN: U4.1 (TXD)
TXDCAN2: U5.1 (TXD)
VIN: C6.1, C7.1, C65.1, C93.1, C106.1, L1.2, U3.2 (VIN), U3.3 (EN)

Notes on the sheet:
Populate if ECU shall be able to keep itself alive after ignition is switched off.
Supply Status LEDs
(3.3V supply indicator in MCU part)
5V Supply
Reverse Protection
Load Dump
Ignition Supply
CAN Transceiver
Input Filter & 5v Regulator
3.3v Supply
TJA1050 (which is LCSC basic part) can be used as drop-in replacement: RXD connected to MCU PB12 (5V tolerant) TJA1050 has logic HIGH-level input voltage of 2.0V at TXD DNP 0R Resistor on VIO in this case!
CAN Transceiver 2
5V Sensor Tracker 1
Main Relay Supply
TJA1050 (which is LCSC basic part) can be used as drop-in replacement: RXD connected to MCU PD0 (5V tolerant) TJA1050 has logic HIGH-level input voltage of 2.0V at TXD DNP 0R Resistor on VIO in this case!
5V Sensor Supply
