tobsec/eidothea/quad_analog.kicad_sch

## KiCad design quad_analog.kicad_sch (2023-04-15)

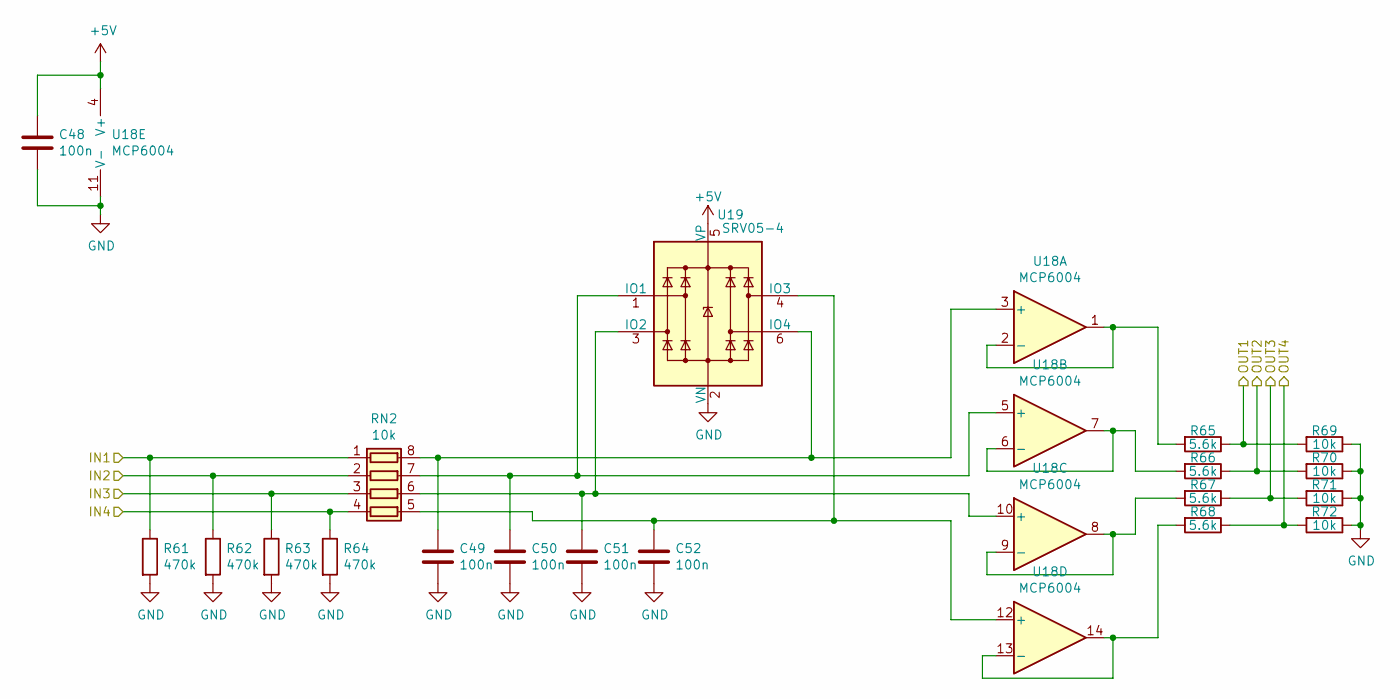
[picture p32: schematic quad_analog.kicad_sch]

Parts:
C48: 100n; C_0603_1608Metric; LCSC C14663
C49, C50, C51, C52: 100n; C_0402_1005Metric; LCSC C1525
R61, R62, R63, R64: 470k; R_0402_1005Metric; LCSC C25790
R65, R66, R67, R68: 5.6k; R_0402_1005Metric; LCSC C25908
R69, R70, R71, R72: 10k; R_0402_1005Metric; LCSC C25744
RN2: 10k; R_Array_Convex_4x0603; LCSC C29718
U18: MCP6004; TSSOP-14_4.4x5mm_P0.65mm; LCSC C50282
U19: SRV05-4; SOT-23-6; LCSC C85364

Connections:
+5V: C48.1, U18.4 (V+), U19.5 (VP)
GND: C48.2, C49.2, C50.2, C51.2, C52.2, R61.2, R62.2, R63.2, R64.2, R69.1, R70.1, R71.1, R72.1, U18.11 (V-), U19.2 (VN)
IN1: R61.1, RN2.1 (R1.1)
IN2: R62.1, RN2.2 (R2.1)
IN3: R63.1, RN2.3 (R3.1)
IN4: R64.1, RN2.4 (R4.1)
unnamed: C49.1, RN2.8 (R1.2), U18.3 (+), U19.6 (IO4)
unnamed: C50.1, RN2.7 (R2.2), U18.5 (+), U19.1 (IO1)
unnamed: C51.1, RN2.6 (R3.2), U18.10 (+), U19.3 (IO2)
unnamed: C52.1, RN2.5 (R4.2), U18.12 (+), U19.4 (IO3)
unnamed: R65.2, U18.1, U18.2 (-)
unnamed: R66.2, U18.6 (-), U18.7
unnamed: R67.2, U18.8, U18.9 (-)
unnamed: R68.2, U18.13 (-), U18.14
OUT1: R65.1, R69.2
OUT2: R66.1, R70.2
OUT3: R67.1, R71.2
OUT4: R68.1, R72.2
