tobsec/eidothea/quad_analog_pullup.kicad_sch

## KiCad design quad_analog_pullup.kicad_sch (2023-04-15)

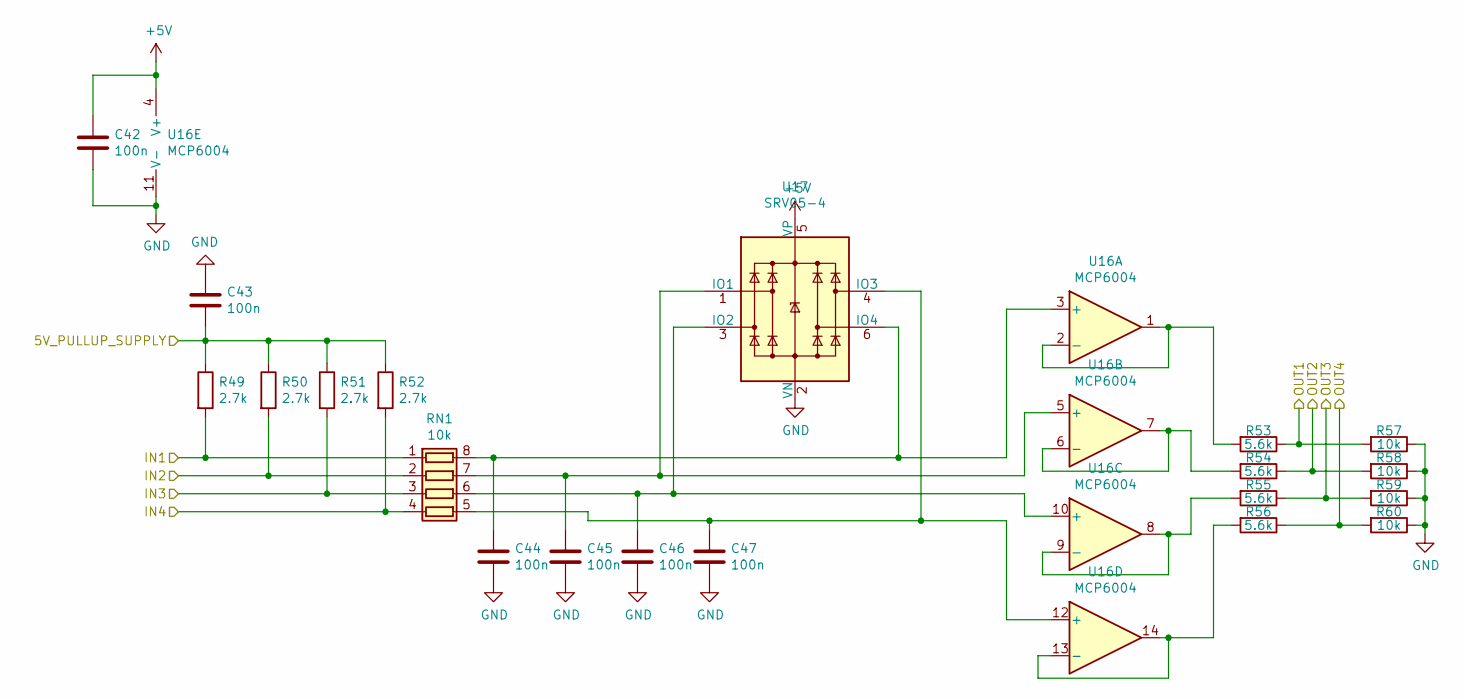
[picture p33: schematic quad_analog_pullup.kicad_sch]

Parts:
C42, C43: 100n; C_0603_1608Metric; LCSC C14663
C44, C45, C46, C47: 100n; C_0402_1005Metric; LCSC C1525
R49, R50, R51, R52: 2.7k; R_0603_1608Metric; LCSC C13167
R53, R54, R55, R56: 5.6k; R_0402_1005Metric; LCSC C25908
R57, R58, R59, R60: 10k; R_0402_1005Metric; LCSC C25744
RN1: 10k; R_Array_Convex_4x0603; LCSC C29718
U16: MCP6004; TSSOP-14_4.4x5mm_P0.65mm; LCSC C50282
U17: SRV05-4; SOT-23-6; LCSC C85364

Connections:
5V_PULLUP_SUPPLY: C43.2, R49.1, R50.1, R51.1, R52.1
+5V: C42.1, U16.4 (V+), U17.5 (VP)
GND: C42.2, C43.1, C44.2, C45.2, C46.2, C47.2, R57.1, R58.1, R59.1, R60.1, U16.11 (V-), U17.2 (VN)
IN1: R49.2, RN1.1 (R1.1)
IN2: R50.2, RN1.2 (R2.1)
IN3: R51.2, RN1.3 (R3.1)
IN4: R52.2, RN1.4 (R4.1)
unnamed: C44.1, RN1.8 (R1.2), U16.3 (+), U17.6 (IO4)
unnamed: C45.1, RN1.7 (R2.2), U16.5 (+), U17.1 (IO1)
unnamed: C46.1, RN1.6 (R3.2), U16.10 (+), U17.3 (IO2)
unnamed: C47.1, RN1.5 (R4.2), U16.12 (+), U17.4 (IO3)
unnamed: R53.2, U16.1, U16.2 (-)
unnamed: R54.2, U16.6 (-), U16.7
unnamed: R55.2, U16.8, U16.9 (-)
unnamed: R56.2, U16.13 (-), U16.14
OUT1: R53.1, R57.2
OUT2: R54.1, R58.2
OUT3: R55.1, R59.2
OUT4: R56.1, R60.2
