tobsec/eidothea/stepper.kicad_sch

## KiCad design stepper.kicad_sch (2023-04-26)

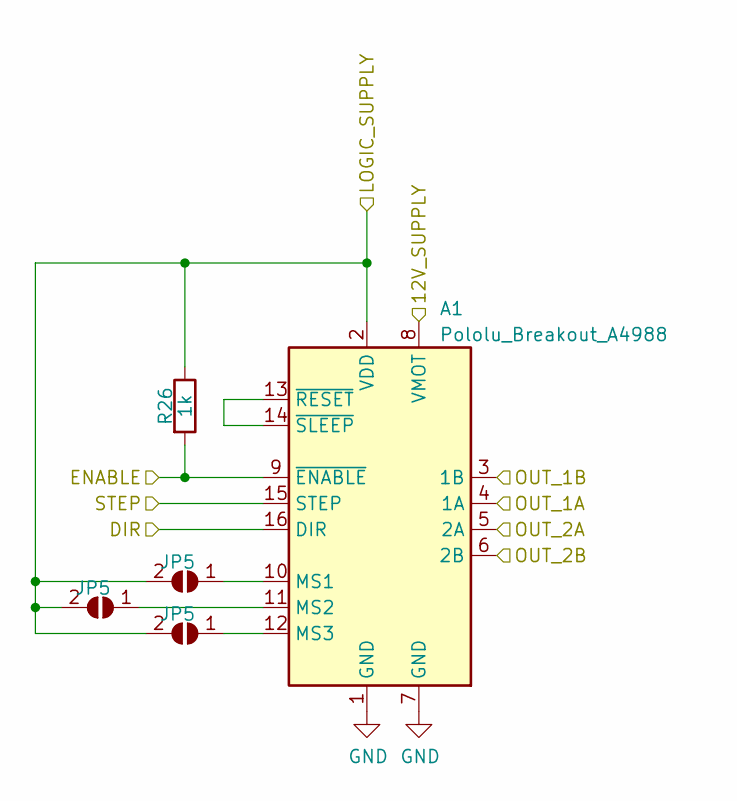
[picture p34: schematic stepper.kicad_sch]

Parts:
A1: Pololu_Breakout_A4988; Pololu_Breakout-16_15.2x20.3mm
JP5: Jumper_2_Bridged; SolderJumper-2_P1.3mm_Open_RoundedPad1.0x1.5mm
R26: 1k; R_0402_1005Metric; LCSC C11702

Connections:
12V_SUPPLY: A1.8 (VMOT)
DIR: A1.16 (DIR)
ENABLE: A1.9 (~ENABLE), R26.2
GND: A1.1 (GND), A1.7 (GND)
LOGIC_SUPPLY: A1.2 (VDD), JP5.2 (B), R26.1
unnamed: A1.10 (MS1), JP5.1 (A)
unnamed: A1.11 (MS2), JP5.1 (A)
unnamed: A1.12 (MS3), JP5.1 (A)
unnamed: A1.13 (~RESET), A1.14 (~SLEEP)
OUT_1A: A1.4 (1A)
OUT_1B: A1.3 (1B)
OUT_2A: A1.5 (2A)
OUT_2B: A1.6 (2B)
STEP: A1.15 (STEP)
