tobsec/eidothea/triggers.kicad_sch

## KiCad design triggers.kicad_sch (2023-04-28)

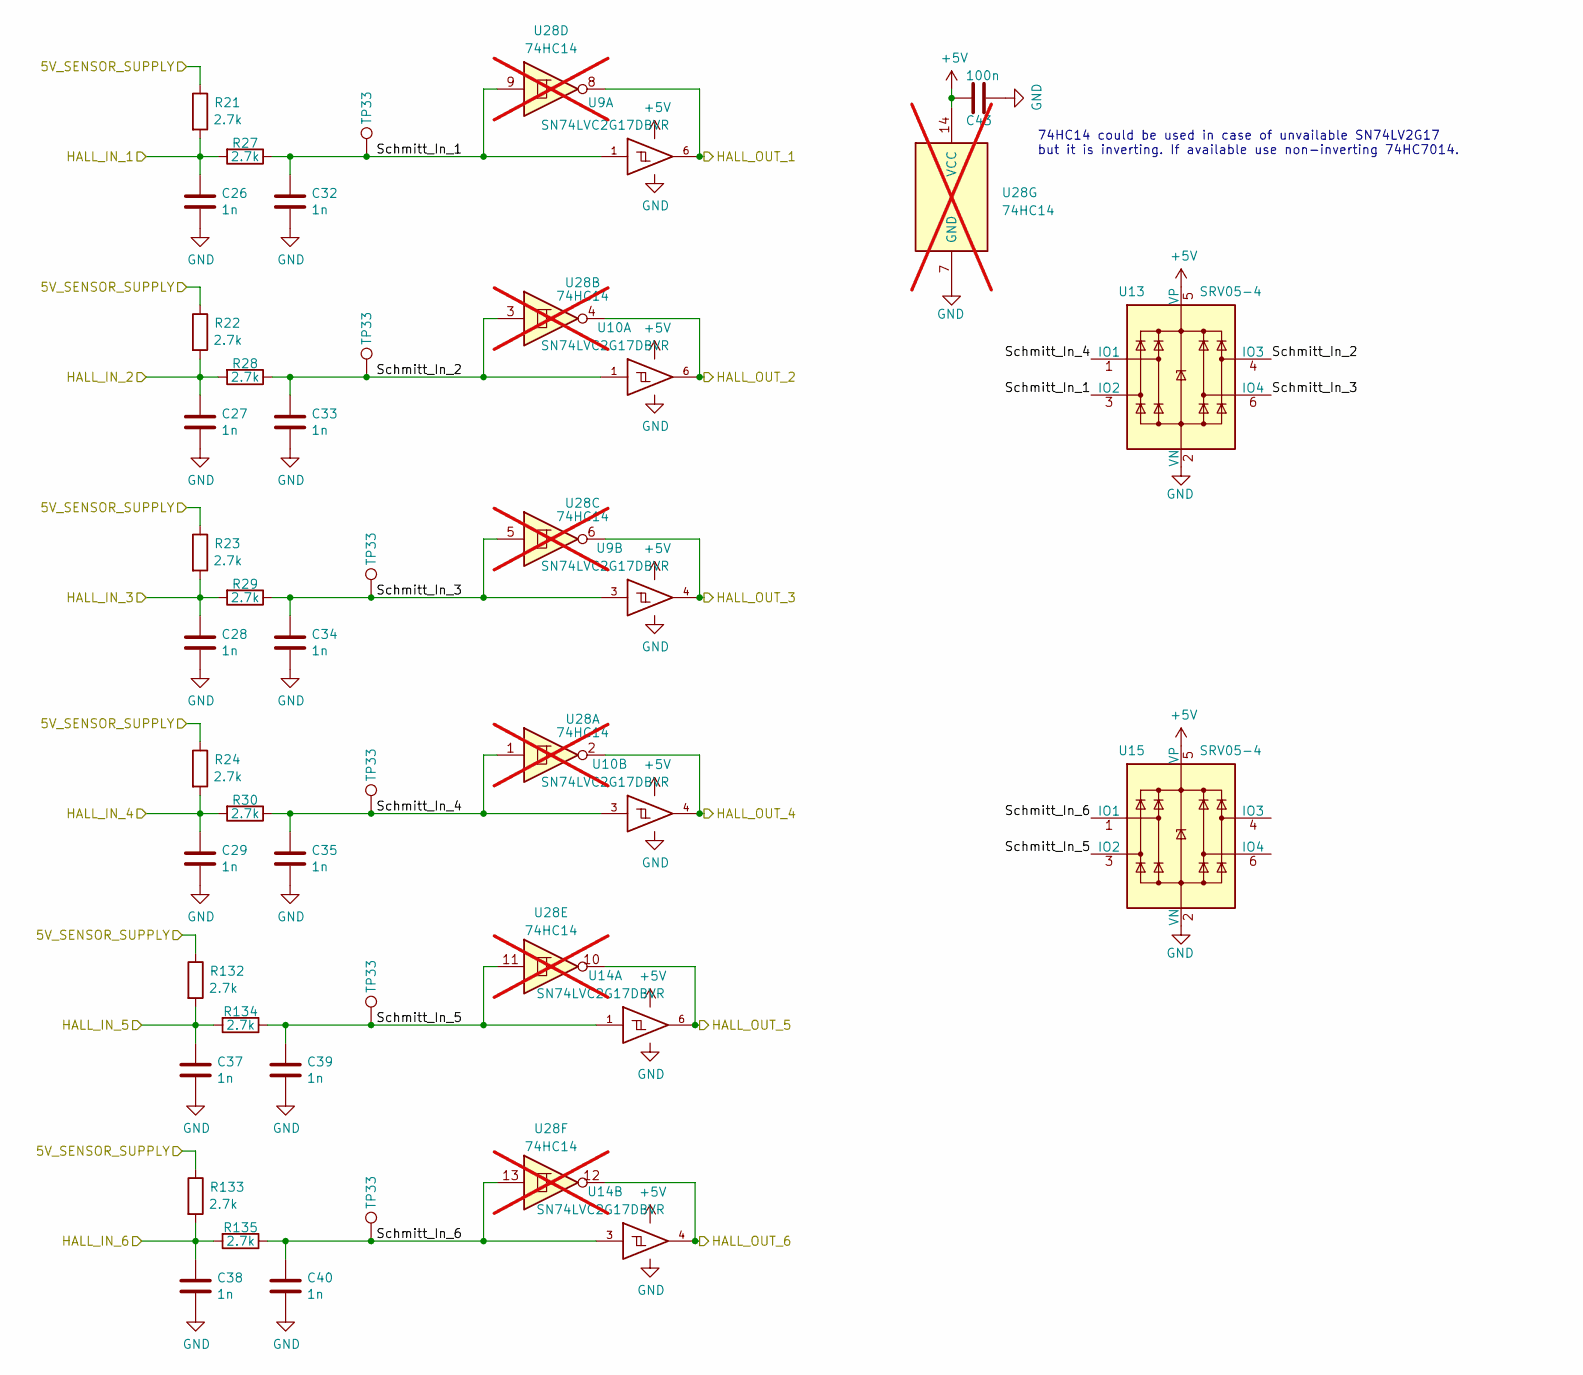
[picture p35: schematic triggers.kicad_sch]

Parts:
C26, C27, C28, C29, C32, C33, C34, C35, C37, C38, C39, C40: 1n; C_0603_1608Metric; LCSC C1588
C43: 100n; C_0603_1608Metric; LCSC C14663
R21, R22, R23, R24, R27, R28, R29, R30, R132, R133, R134, R135: 2.7k; R_0603_1608Metric; LCSC C13167
TP33: TestPoint; TestPoint_Pad_D1.0mm
U9, U10, U14: SN74LVC2G17DBVR; SOT-23-6; LCSC C10429
U13, U15: SRV05-4; SOT-23-6; LCSC C85364
U28: 74HC14; SOIC-14_3.9x8.7mm_P1.27mm; not fitted

Connections:
5V_SENSOR_SUPPLY: R21.1, R22.1, R23.1, R24.1, R132.1, R133.1
+5V: C43.2, U9.5 (VCC), U10.5 (VCC), U13.5 (VP), U14.5 (VCC), U15.5 (VP), U28.14 (VCC)
GND: C26.2, C27.2, C28.2, C29.2, C32.2, C33.2, C34.2, C35.2, C37.2, C38.2, C39.2, C40.2, C43.1, U9.2 (GND), U10.2 (GND), U13.2 (VN), U14.2 (GND), U15.2 (VN), U28.7 (GND)
HALL_IN_1: C26.1, R21.2, R27.2
HALL_IN_2: C27.1, R22.2, R28.2
HALL_IN_3: C28.1, R23.2, R29.2
HALL_IN_4: C29.1, R24.2, R30.2
HALL_IN_5: C37.1, R132.2, R134.2
HALL_IN_6: C38.1, R133.2, R135.2
HALL_OUT_1: U9.6, U28.8
HALL_OUT_2: U10.6, U28.4
HALL_OUT_3: U9.4, U28.6
HALL_OUT_4: U10.4, U28.2
HALL_OUT_5: U14.6, U28.10
HALL_OUT_6: U14.4, U28.12
Schmitt_In_1: C32.1, R27.1, TP33.1, U9.1, U13.3 (IO2), U28.9
Schmitt_In_2: C33.1, R28.1, TP33.1, U10.1, U13.4 (IO3), U28.3
Schmitt_In_3: C34.1, R29.1, TP33.1, U9.3, U13.6 (IO4), U28.5
Schmitt_In_4: C35.1, R30.1, TP33.1, U10.3, U13.1 (IO1), U28.1
Schmitt_In_5: C39.1, R134.1, TP33.1, U14.1, U15.3 (IO2), U28.11
Schmitt_In_6: C40.1, R135.1, TP33.1, U14.3, U15.1 (IO1), U28.13

Notes on the sheet:
74HC14 could be used in case of unvailable SN74LV2G17 but it is inverting. If available use non-inverting 74HC7014.
